mohammedryn/digikey-hackathon-submission/firmware/schematic/digikey.kicad_sch

## KiCad design firmware/schematic/digikey.kicad_sch (2026-02-15)

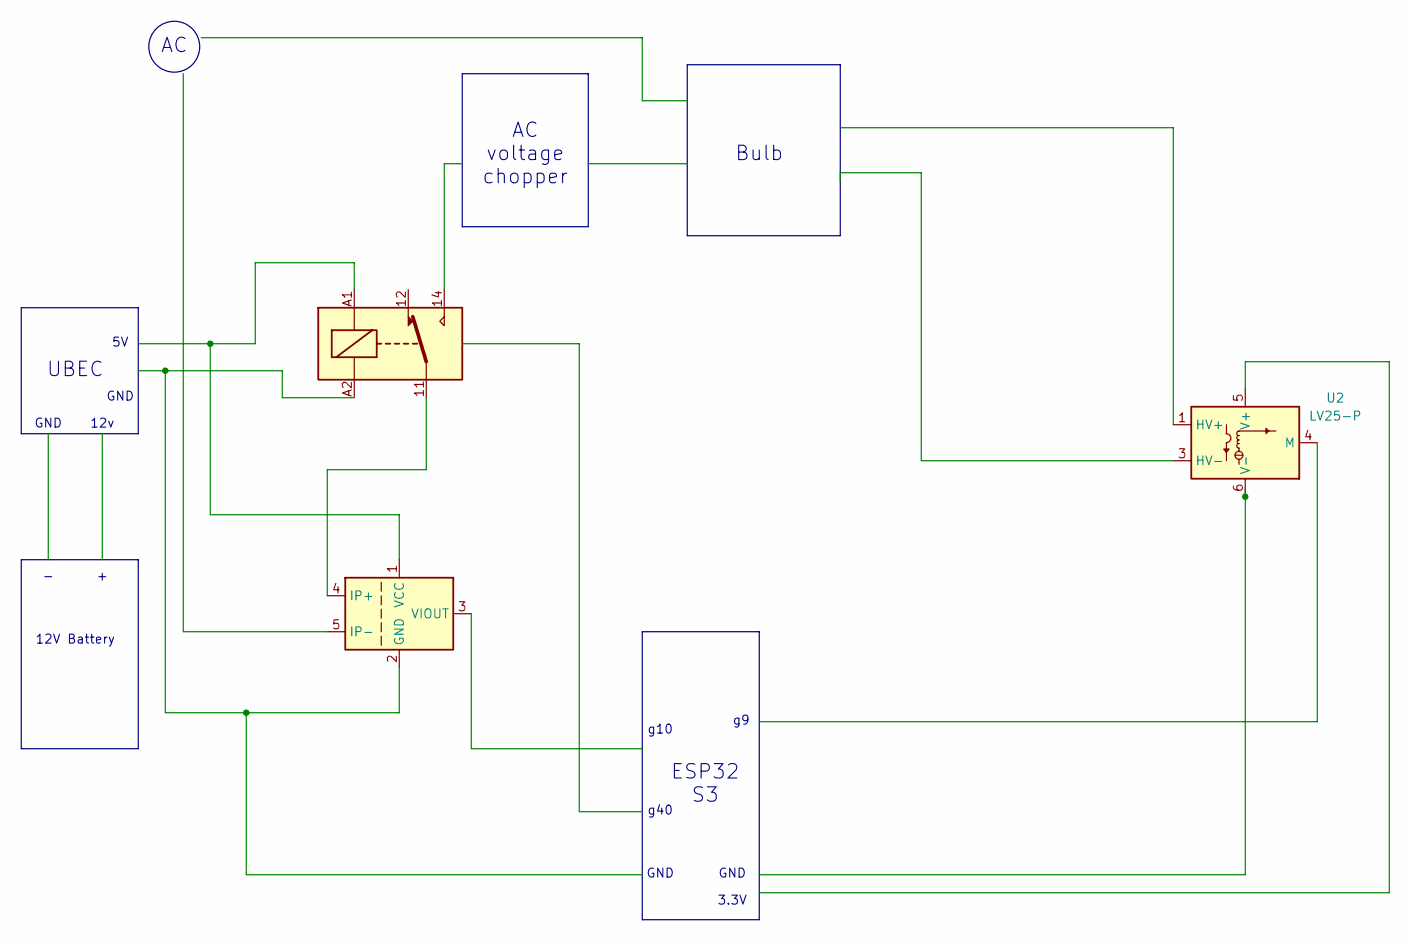
[picture p3: schematic digikey.kicad_sch]

Parts:
K1: Fujitsu_FTR-LYCA005x; Relay_SPDT_Fujitsu_FTR-LYCA005x_FormC_Vertical
U1: ACS756xCB-100B-PFF; Allegro_CB_PFF
U2: LV25-P; LEM_LV25-P

Connections:
unnamed: K1.11, U1.4 (IP+)
unnamed: K1.A1, U1.1 (VCC)
unnamed: K1.A2, U1.2 (GND)

Notes on the sheet:
12v
GND
g10
12V Battery
Bulb
3.3V
AC voltage chopper
ESP32 S3
UBEC
g40
